cormoran/dya-dash-keyboard/docs/src/assets/header.jpeg

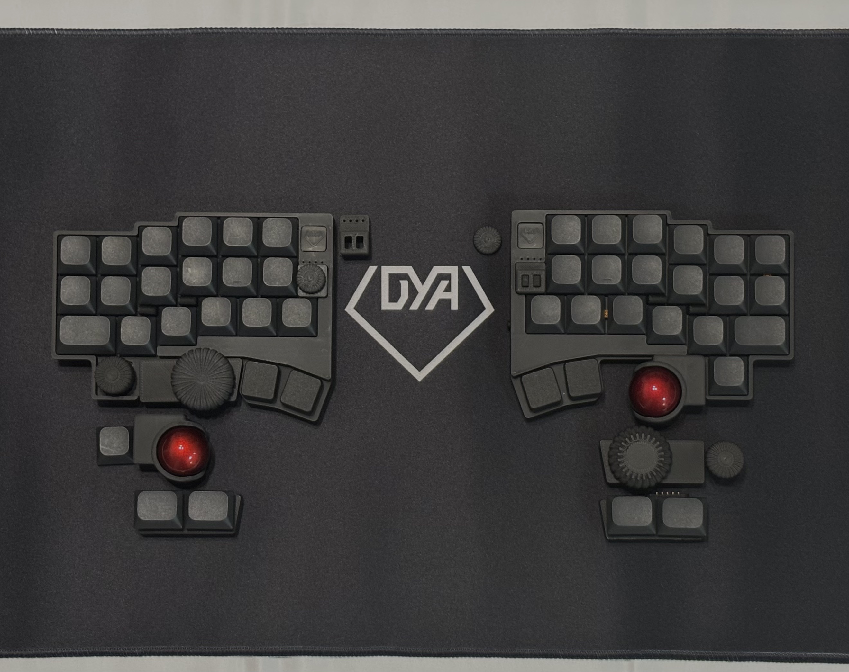
docs/src/assets/header.jpeg
