cormoran/dya-dash-keyboard/powerprofile/Rainbow.png

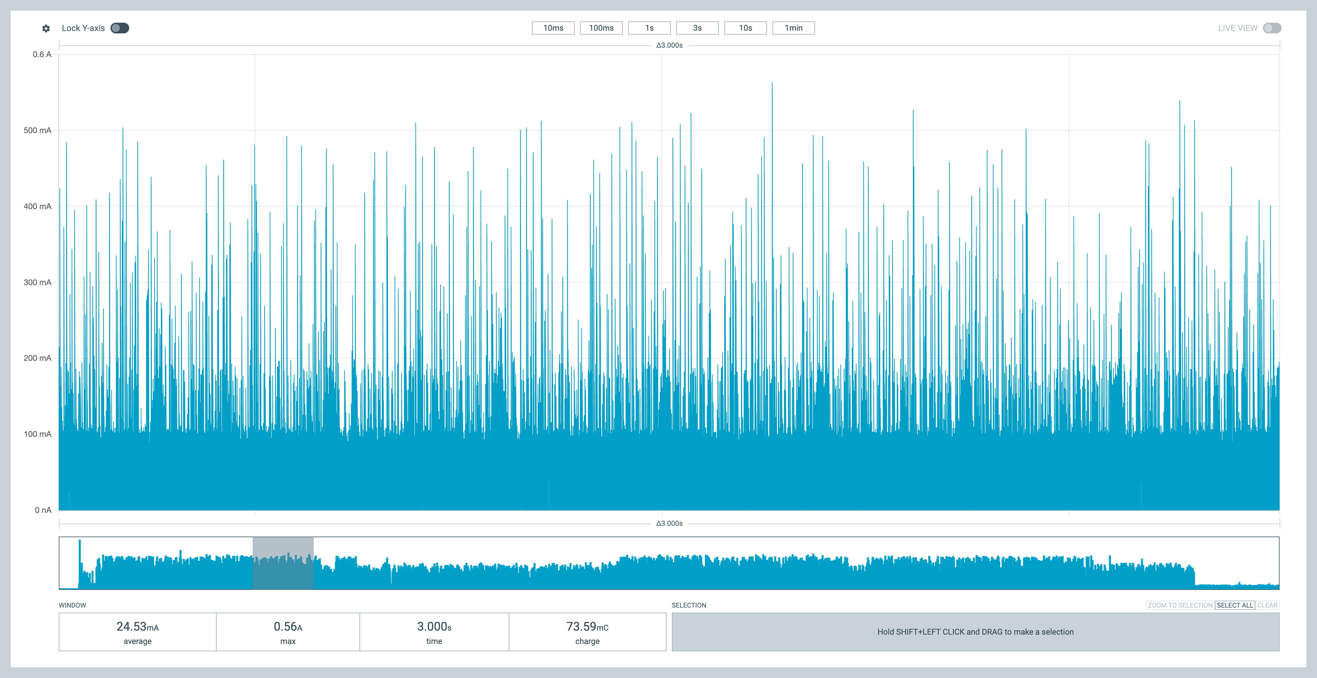
powerprofile/Rainbow.png
