cormoran/dya-dash-keyboard/hardware/dya-dash/case/V1/arrow-button.stl

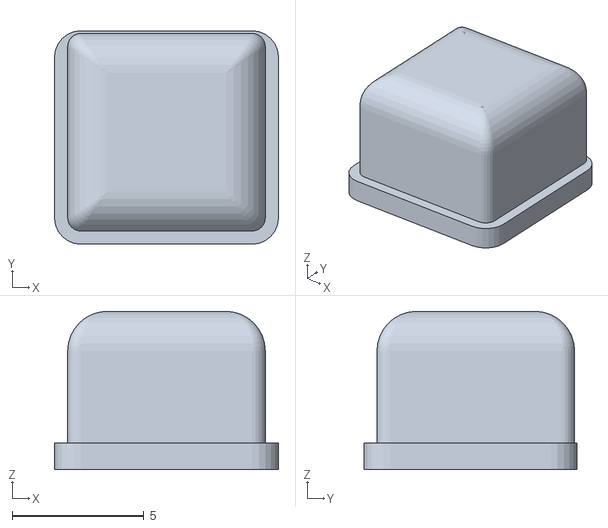
[picture p28: CAD file, 2025-06-15, an earlier design]
hardware/dya-dash/case/V1/arrow-button.stl
8.50 x 8.10 x 6.00
