cormoran/dya-dash-keyboard/docs/src/content/docs/build-guide/v3/img/encoderkit/left.jpeg

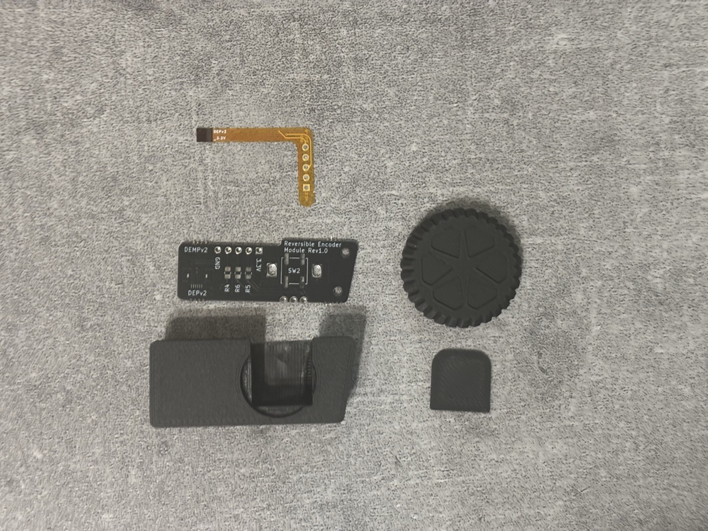
docs/src/content/docs/build-guide/v3/img/encoderkit/left.jpeg
