cormoran/dya-dash-keyboard/docs/src/content/docs/build-guide/v3/img/encoderkit/right.jpeg

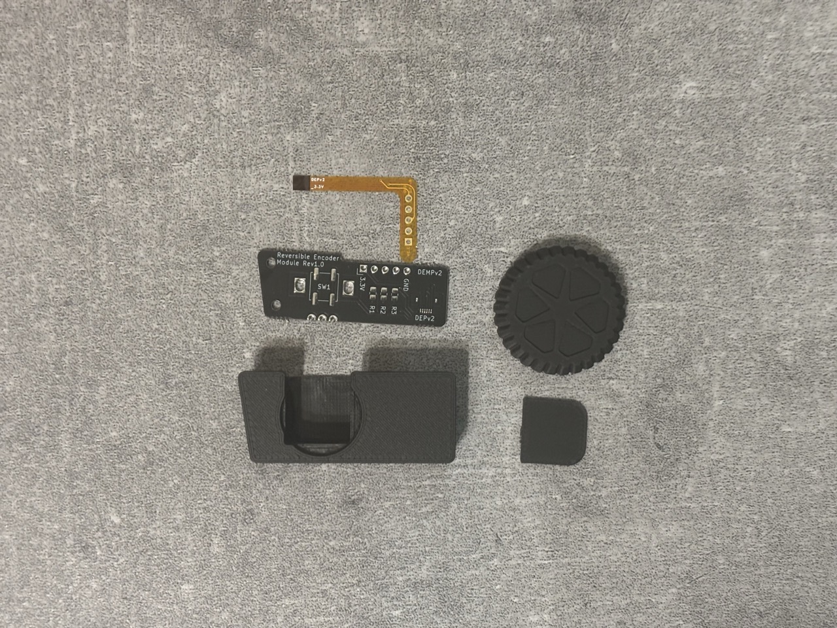
docs/src/content/docs/build-guide/v3/img/encoderkit/right.jpeg
